MKD-software/CorroSenseBoardV4/measurements/sweep_100.0_200.0_10steps_100ms_DDS255_TIA255.png

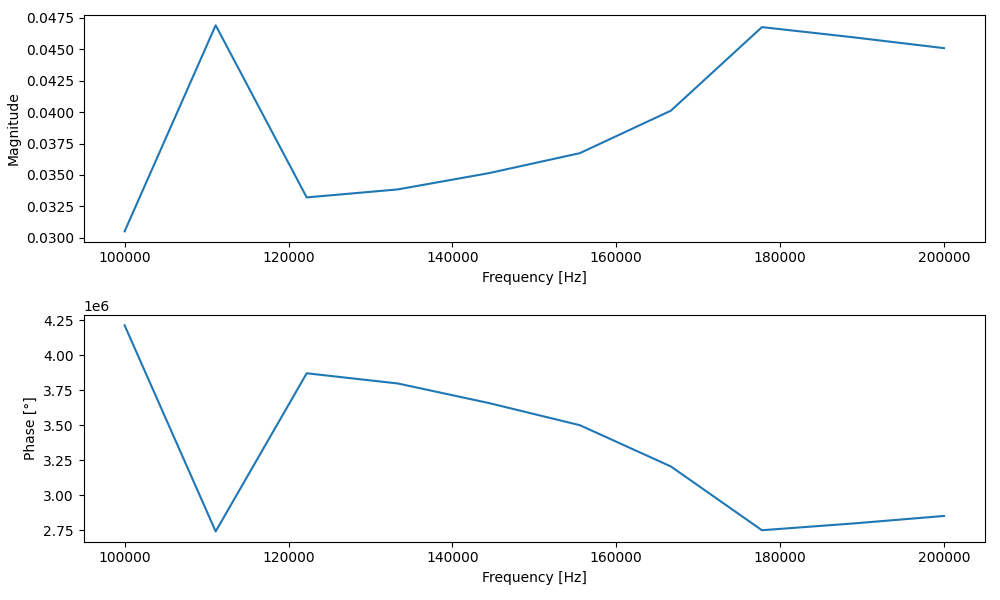
measurements/sweep_100.0_200.0_10steps_100ms_DDS255_TIA255.png
