MKD-software/CorroSenseBoardV4/measurements/TIA test/sweep_100.0_271.0_2140res_2ms_DDS10_TIA4.csv

Frequency [Hz] | Magnitude | Phase [°]
100000 | 32767 | 32767
100214 | 32767 | 32767
100428 | 32767 | 32767
100642 | 32767 | 32767
100856 | 32767 | 32767
101070 | 32767 | 32767
101284 | 32767 | 32767
101498 | 32767 | 32767
101712 | 32767 | 32767
101926 | 32767 | 32767
102140 | 32767 | 32767
102354 | 32767 | 32767
102568 | 32767 | 32767
102782 | 32767 | 32767
102996 | 32767 | 32767
103210 | 32767 | 32767
103424 | 32767 | 32767
103638 | 32767 | 32767
103852 | 32767 | 32767
104066 | 32767 | 32767
104280 | 32767 | 32767
104494 | 32767 | 32767
104708 | 32767 | 32767
104922 | 32767 | 32767
105136 | 32767 | 32767
105350 | 32767 | 32767
105564 | 32767 | 32767
105778 | 32767 | 32767
105992 | 32767 | 32767
106206 | 32767 | 32767
106420 | 32767 | 32767
106634 | 32767 | 32767
106848 | 32767 | 32767
107062 | 32767 | 32767
107276 | 32767 | 32767
107490 | 32767 | 32767
107704 | 32767 | 32767
107918 | 32767 | 32767
108132 | 32767 | 32767
108346 | 32767 | 32767
108560 | 32767 | 32767
108774 | 32767 | 32767
108988 | 32767 | 32767
109202 | 32767 | 32767
109416 | 32767 | 32767
109630 | 32767 | 32767
109844 | 32767 | 32767
110058 | 32767 | 32767
110272 | 32767 | 32767
110486 | 32767 | 32767
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
