MKD-software/CorroSenseBoardV4/measurements/TIA test/sweep_20.0_91.0_3568res_2ms_DDS10_TIA1.csv

Frequency [Hz] | Magnitude | Phase [°]
20000 | 32767 | 32767
20356 | 22564 | 22564
20713 | 22560 | 22560
21070 | 22561 | 22561
21427 | 22552 | 22552
21784 | 22550 | 22550
22140 | 22548 | 22548
22497 | 22538 | 22538
22854 | 22535 | 22535
23211 | 22529 | 22529
23568 | 22526 | 22526
23924 | 22515 | 22515
24281 | 22507 | 22507
24638 | 22504 | 22504
24995 | 22497 | 22497
25352 | 22484 | 22484
25708 | 22477 | 22477
26065 | 22473 | 22473
26422 | 22464 | 22464
26779 | 22452 | 22452
27136 | 22445 | 22445
27492 | 22441 | 22441
27849 | 22429 | 22429
28206 | 22422 | 22422
28563 | 22421 | 22421
28920 | 22410 | 22410
29276 | 22408 | 22408
29633 | 22409 | 22409
29990 | 22404 | 22404
30347 | 22459 | 22459
30704 | 22407 | 22407
31060 | 22402 | 22402
31417 | 23118 | 23118
31774 | 22795 | 22795
32131 | 22404 | 22404
32488 | 22411 | 22411
32844 | 22406 | 22406
33201 | 22402 | 22402
33558 | 22707 | 22707
33915 | 22407 | 22407
34272 | 22403 | 22403
34628 | 22449 | 22449
34985 | 23281 | 23281
35342 | 22516 | 22516
35699 | 22856 | 22856
36056 | 22409 | 22409
36412 | 22743 | 22743
36769 | 23219 | 23219
37126 | 22591 | 22591
37483 | 22461 | 22461
37840 | 22469 | 22469
38196 | 22850 | 22850
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
