MKD-software/CorroSenseBoardV4/measurements/TIA test/sweep_20.0_91.0_3568res_2ms_DDS10_TIA2.csv

Frequency [Hz] | Magnitude | Phase [°]
20000 | 32767 | 32767
20356 | 22827 | 22827
20713 | 22828 | 22828
21070 | 22822 | 22822
21427 | 22807 | 22807
21784 | 22805 | 22805
22140 | 22795 | 22795
22497 | 22787 | 22787
22854 | 22768 | 22768
23211 | 22767 | 22767
23568 | 22755 | 22755
23924 | 22736 | 22736
24281 | 22721 | 22721
24638 | 22713 | 22713
24995 | 22694 | 22694
25352 | 22667 | 22667
25708 | 22656 | 22656
26065 | 22642 | 22642
26422 | 22626 | 22626
26779 | 22598 | 22598
27136 | 22582 | 22582
27492 | 22570 | 22570
27849 | 22543 | 22543
28206 | 22525 | 22525
28563 | 22514 | 22514
28920 | 22496 | 22496
29276 | 22470 | 22470
29633 | 22462 | 22462
29990 | 22447 | 22447
30347 | 22429 | 22429
30704 | 22427 | 22427
31060 | 22411 | 22411
31417 | 22721 | 22721
31774 | 22407 | 22407
32131 | 23285 | 23285
32488 | 23315 | 23315
32844 | 22939 | 22939
33201 | 22921 | 22921
33558 | 22400 | 22400
33915 | 22583 | 22583
34272 | 22393 | 22393
34628 | 22690 | 22690
34985 | 22649 | 22649
35342 | 24010 | 24010
35699 | 22404 | 22404
36056 | 25158 | 25158
36412 | 22642 | 22642
36769 | 23322 | 23322
37126 | 23441 | 23441
37483 | 23434 | 23434
37840 | 23704 | 23704
38196 | 22439 | 22439
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
