MKD-software/CorroSenseBoardV4/measurements/dwell test/sweep_20.0_271.0_278889res_2ms_DDS255_TIA1.png

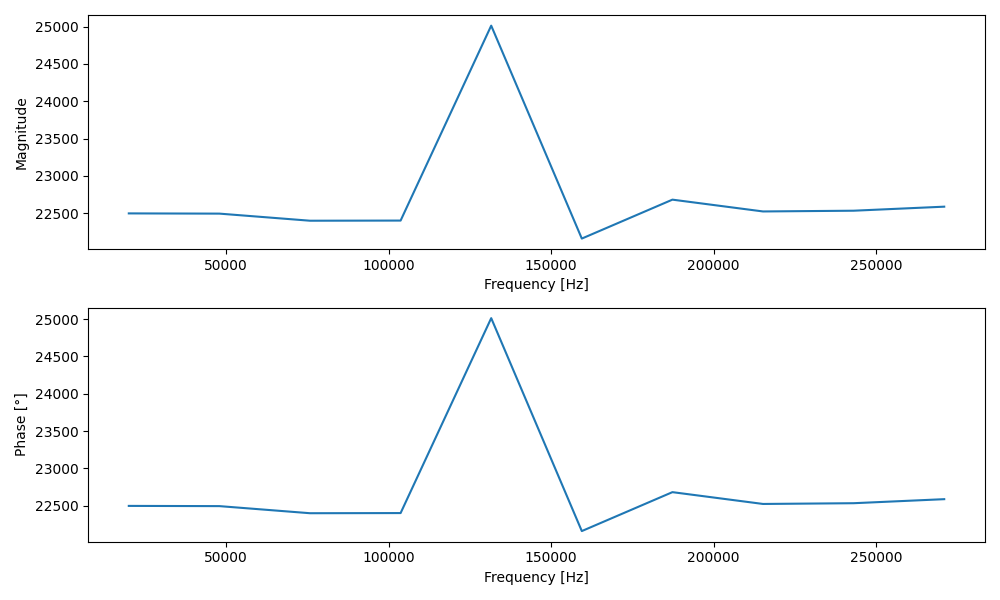
measurements/dwell test/sweep_20.0_271.0_278889res_2ms_DDS255_TIA1.png
