MKD-software/CorroSenseBoardV4/measurements/dwell test/sweep_200.0_271.0_1423res_0ms_DDS255_TIA2.png

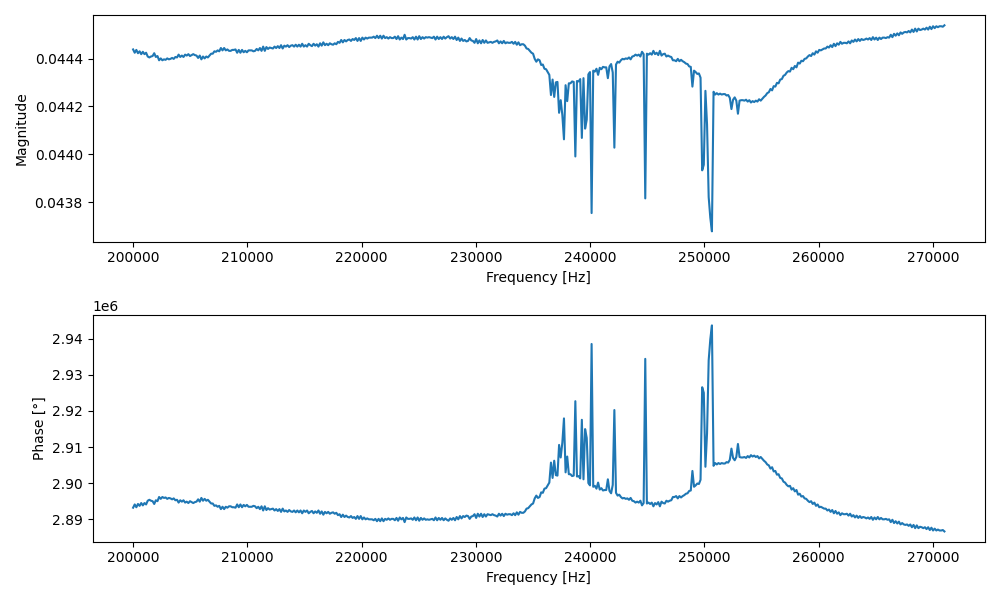
measurements/dwell test/sweep_200.0_271.0_1423res_0ms_DDS255_TIA2.png
