MKD-software/CorroSenseBoardV4/measurements/dwell test/sweep_200.0_271.0_3568res_2ms_DDS10_TIA3.png

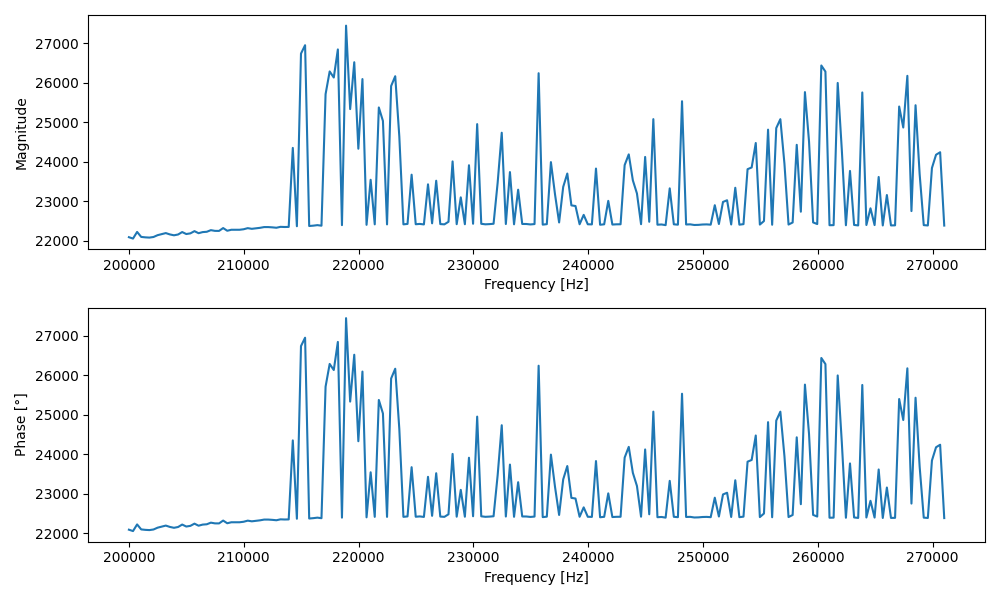
measurements/dwell test/sweep_200.0_271.0_3568res_2ms_DDS10_TIA3.png
