MKD-software/CorroSenseBoardV4/measurements/dwell test/sweep_200.0_271.0_3568res_2ms_DDS255_TIA1.png

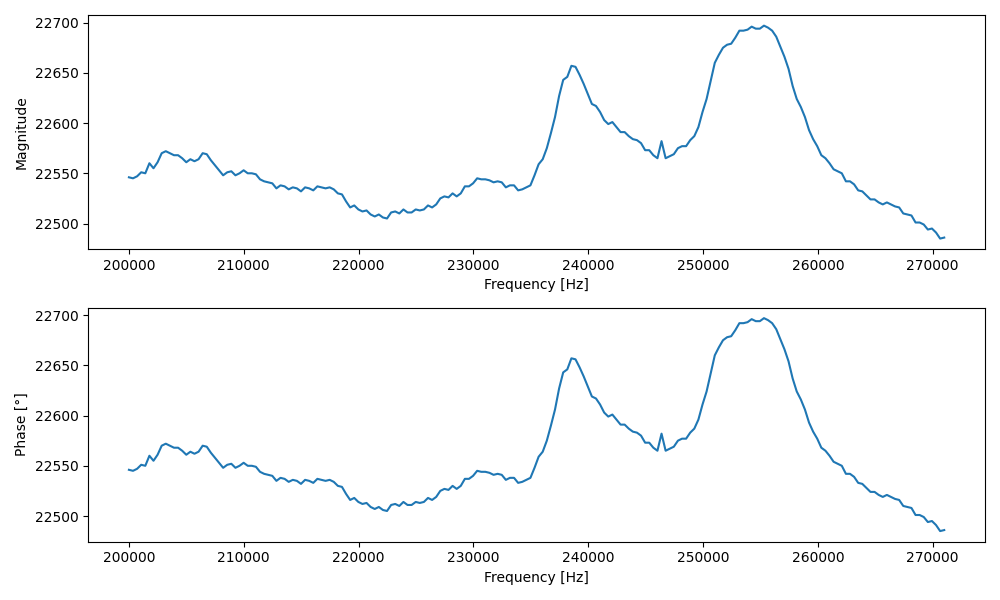
measurements/dwell test/sweep_200.0_271.0_3568res_2ms_DDS255_TIA1.png
