MKD-software/CorroSenseBoardV4/measurements/sweep_100.0_200.0_1001res_10ms_DDS255_TIA255.png

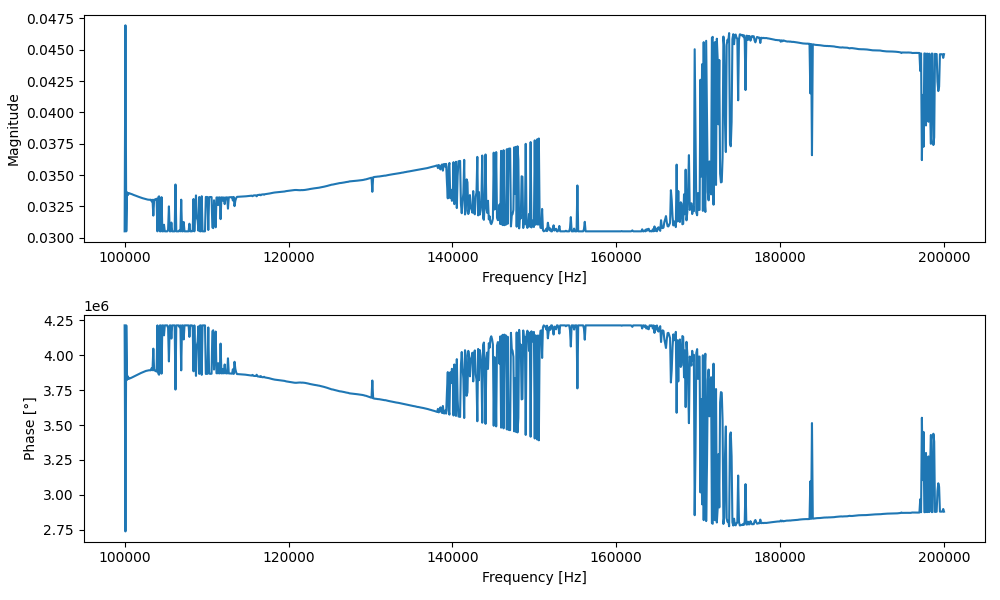
measurements/sweep_100.0_200.0_1001res_10ms_DDS255_TIA255.png
