MKD-software/CorroSenseBoardV4/measurements/TIA test/sweep_20.0_91.0_3568res_2ms_DDS10_TIA2.png

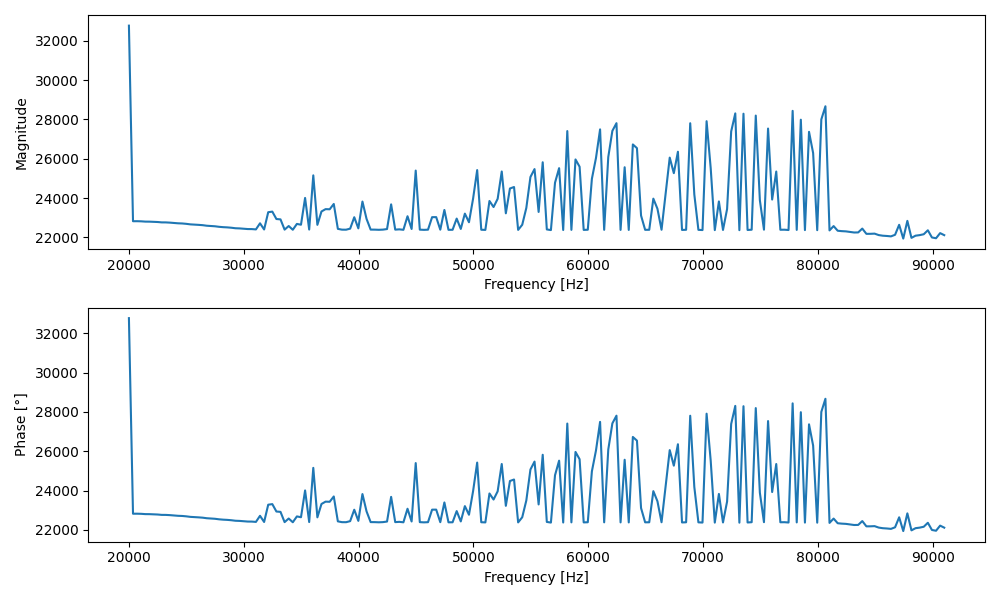
measurements/TIA test/sweep_20.0_91.0_3568res_2ms_DDS10_TIA2.png
