MKD-software/CorroSenseBoardV4/measurements/TIA test/sweep_100.0_271.0_2140res_2ms_DDS10_TIA3.png

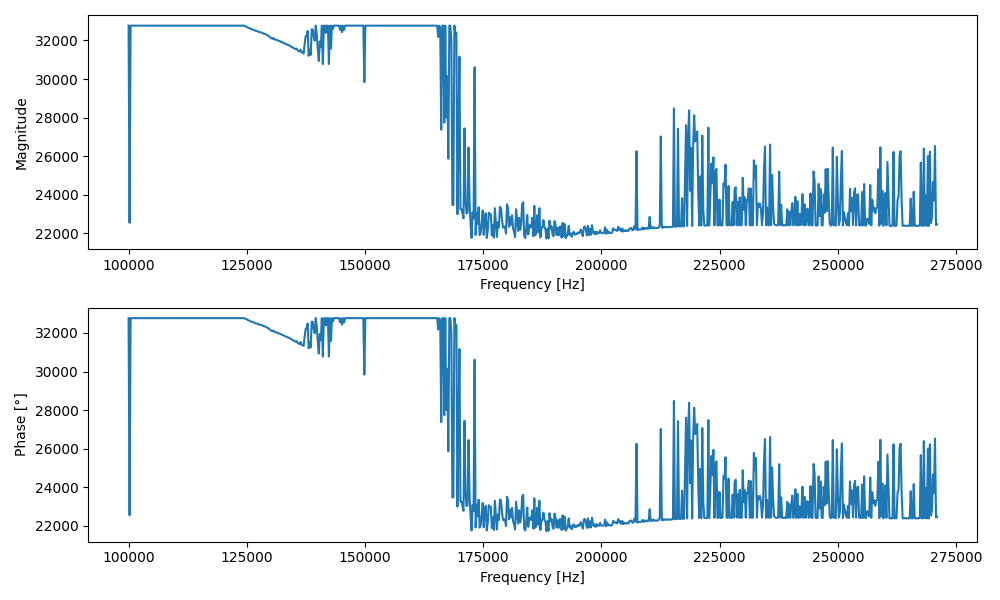
measurements/TIA test/sweep_100.0_271.0_2140res_2ms_DDS10_TIA3.png
