MKD-software/CorroSenseBoardV4/measurements/TIA test/sweep_200.0_271.0_3568res_2ms_DDS10_TIA1.png

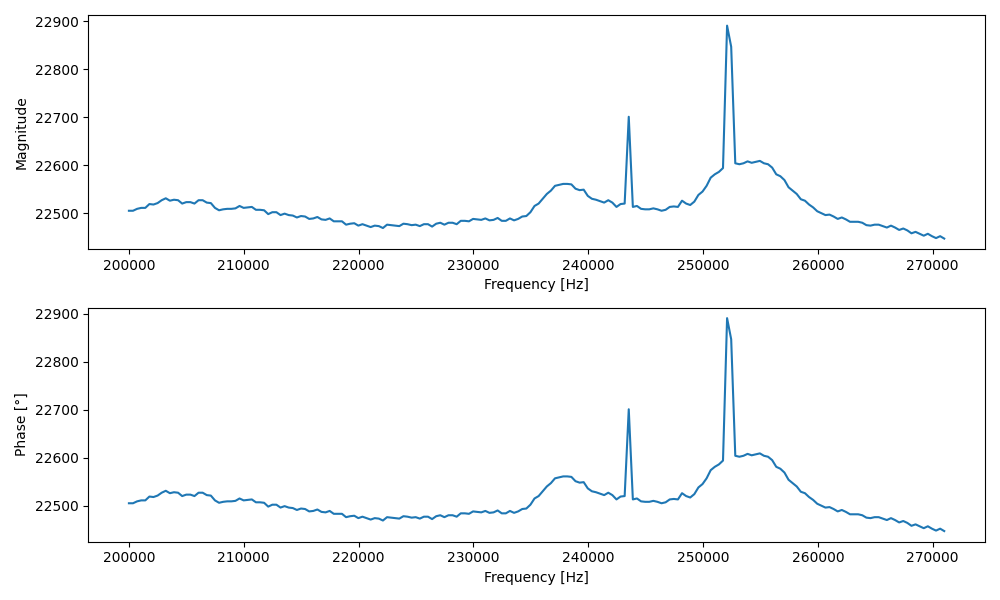
measurements/TIA test/sweep_200.0_271.0_3568res_2ms_DDS10_TIA1.png
