MKD-software/CorroSenseBoardV4/measurements/TIA test/sweep_200.0_350.0_2504res_2ms_DDS10_TIA2.png

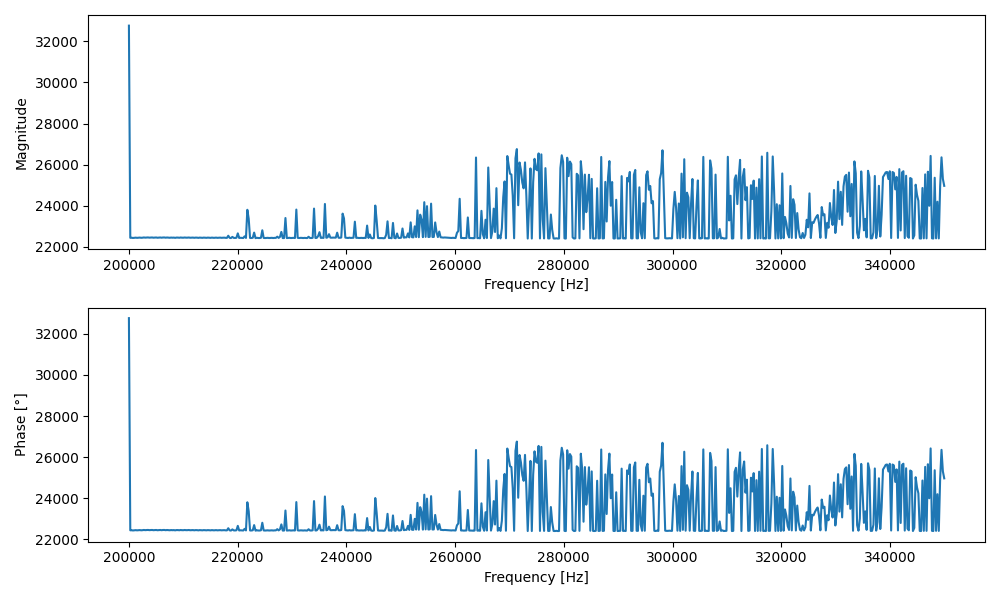
measurements/TIA test/sweep_200.0_350.0_2504res_2ms_DDS10_TIA2.png
